OLIMEX/eduArdu/SOFTWARE/5_eduArdu_Microphone/5_eduArdu_Microphone.ino

/**********************************************************************
Demo example for Olimex board eduArdu
Tested with Arduino 1.8.8
Date: 2018/12/12

Description:
A simple demo that toggles the builtin LED (D12) when detects noise.
**********************************************************************/

#define LED 12
#define MICROPHONE  A3

#define THRESHOLD 75  // higher value means less sensitivity

void setup()
{
  pinMode(LED, OUTPUT);
  digitalWrite (LED, LOW);
  Serial.begin(115200);
}

void loop()
{
  int Max=0, Min=1024;
  for(int i=0; i<50; i++) // taking a sequence of samples to determine whether there is noise or not
  {
    int Sample;
    Sample = analogRead(MICROPHONE);
    if (Sample > Max)
      Max = Sample;

    if (Sample < Min)
      Min = Sample;

    Serial.println(Max-Min);
    
    if((Max-Min) > THRESHOLD)
    {
      digitalWrite (LED, !digitalRead(LED));
      delay(100);
      break;
    }
  }
  
}
