OLIMEX/eduArdu/SOFTWARE/2_eduArdu_Buzzer/Tracks/All_Tracks.h

#ifndef	_ALL_TRACKS_H
#define	_ALL_TRACKS_H


#include "Imperial_March.h"
#include "Amazing_Grace.h"
#include "Mario_Bros.h"
#include "Mario_Bros_Underwater.h"
#include "Silent_Night_Holy_Night.h"

#endif
