OLIMEX/eduArdu/SOFTWARE/2_eduArdu_Buzzer/Tracks/Mario_Bros.h

#ifndef	_MARIO_BROS_H
#define	_MARIO_BROS_H



int MB1_Tempo = 200;
const int   MB1_Note[] =     {_e7, _e7, _P, _e7, _P, _c7, _e7, _P, _g7, _P, _P, _P, _g6, _P, _P, _P, _c7, _P, _P, _g6, _P, _P, _e6, _P, _P, _a6, _P, _b6, _P, _bB6, _a6, _P, _END};
const float MB1_Duration[] = {_8 , _8 , _8, _8 , _8, _8 , _8 , _8, _8 , _8, _8, _8, _8 , _8, _8, _8, _8 , _8, _8, _8 , _8, _8, _8 , _8, _8, _8 , _8, _8 , _8, _8  , _8 , _8, _END};

int MB2_Tempo = 200;
const int   MB2_Note[] =     {_g6, _e7, _P , _g7, _a7, _P, _f7, _g7, _P, _e7, _P, _c7, _d7, _b6, _P, _P, _END};
const float MB2_Duration[] = {_8 , _8 , _8 , _8 , _8 , _8, _8 , _8 , _8, _8 , _8, _8 , _8 , _8 , _8, _8, _END};

int MB3_Tempo = 200;
const int   MB3_Note[] =     {_c7, _P, _P, _g6, _P, _P, _e6, _P, _P, _a6, _P, _b6, _P, _bB6, _a6, _P, _END};
const float MB3_Duration[] = {_8 , _8, _8, _8 , _8, _8, _8 , _8, _8, _8 , _8, _8 , _8, _8  , _8 , _8, _END};

int MB4_Tempo = 200;
const int   MB4_Note[] =     {_g6, _e7, _P, _g7, _a7, _P, _f7, _g7, _P, _e7, _P, _c7, _d7, _b6, _P, _P, _END};
const float MB4_Duration[] = {_8 , _8 , _8, _8 , _8 , _8, _8 , _8 , _8, _8 , _8, _8 , _8 , _8 , _8, _8, _END};

#endif
